AdrianHettler/battery-canister-36c/mechanical/pictures/2.png

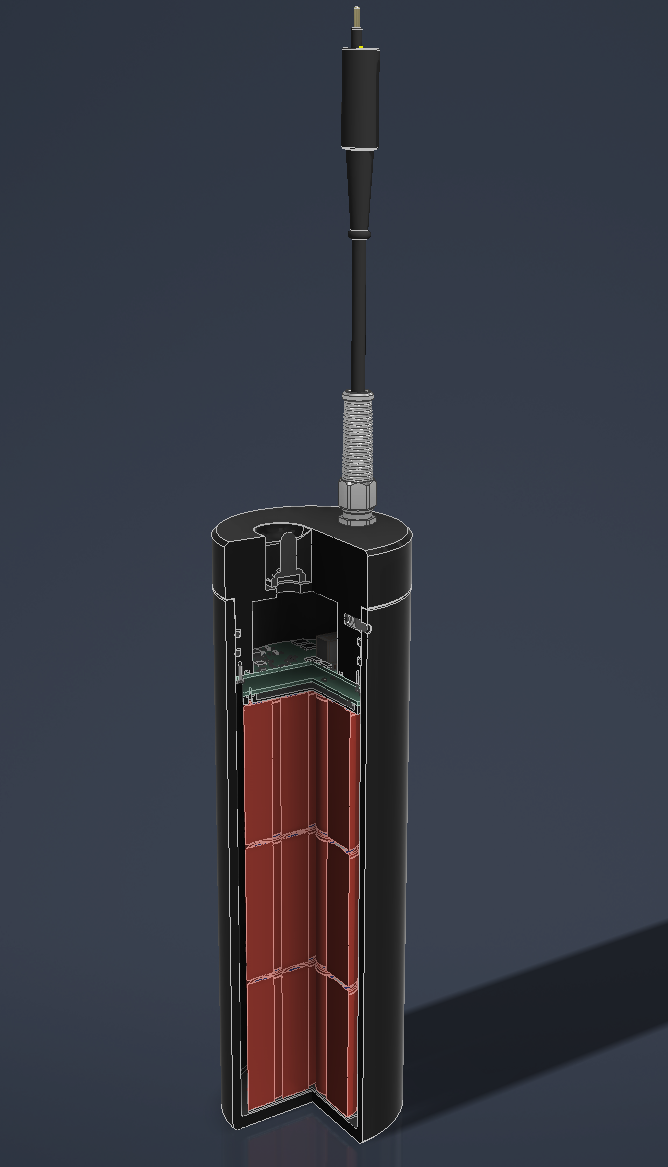
mechanical/pictures/2.png
